boyuanxiao/SolarTracker/pcb/photodiode.sch

## KiCad design pcb/photodiode.sch (2017-03-01, an earlier design)

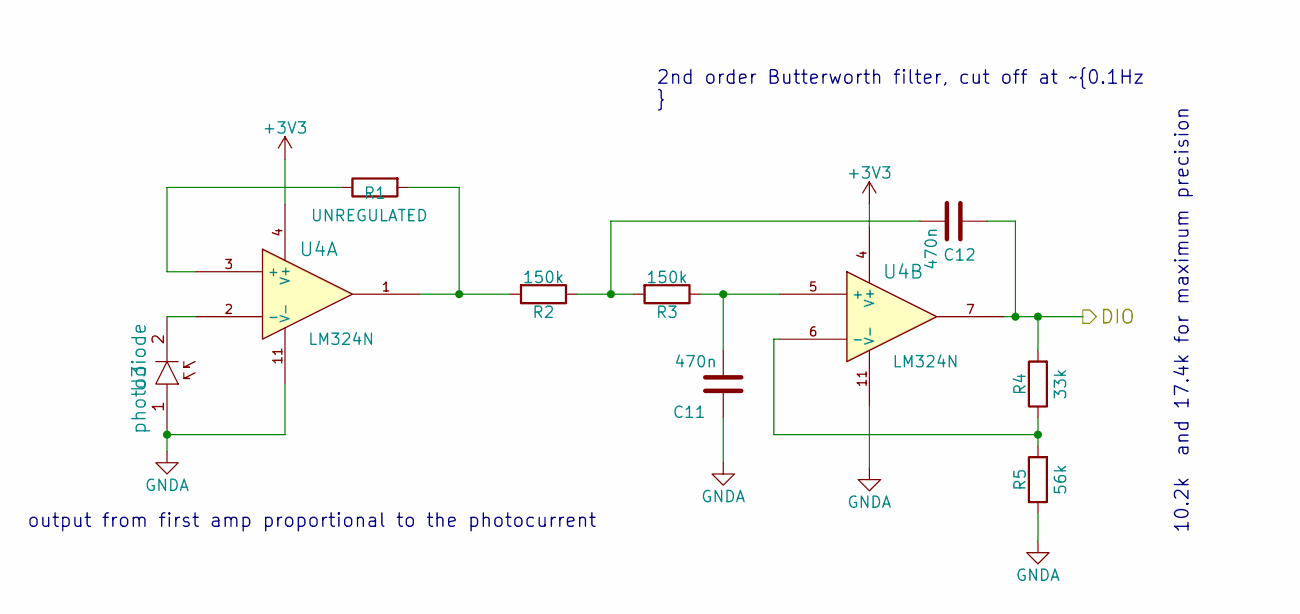
[picture p16: schematic photodiode.sch]

Parts:
C11, C16: 470n
R11: UNREGULATED
R12, R13: 150k
R14: 33k
R15: 56k
U6: photodiode
U7: LM324N

Connections:
+3V3: U7.4 (V+)
DIO: C16.1, R14.2, U7.7
GNDA: C11.1, R15.1, U6.1 (A), U7.11 (V-)
unnamed: C11.2, R13.1, U7.5 (+)
unnamed: C16.2, R12.1, R13.2
unnamed: R11.1, U7.3 (+)
unnamed: R11.2, R12.2, U7.1
unnamed: R14.1, R15.2, U7.6 (-)
unnamed: U6.2 (C), U7.2 (-)

Notes on the sheet:
2nd order Butterworth filter, cut off at ~0.1Hz
output from first amp proportional to the photocurrent
10.2k and 17.4k for maximum precision
