boyuanxiao/SolarTracker/pcb/solarTracker.sch

## KiCad design pcb/solarTracker.sch (2017-03-01, an earlier design)

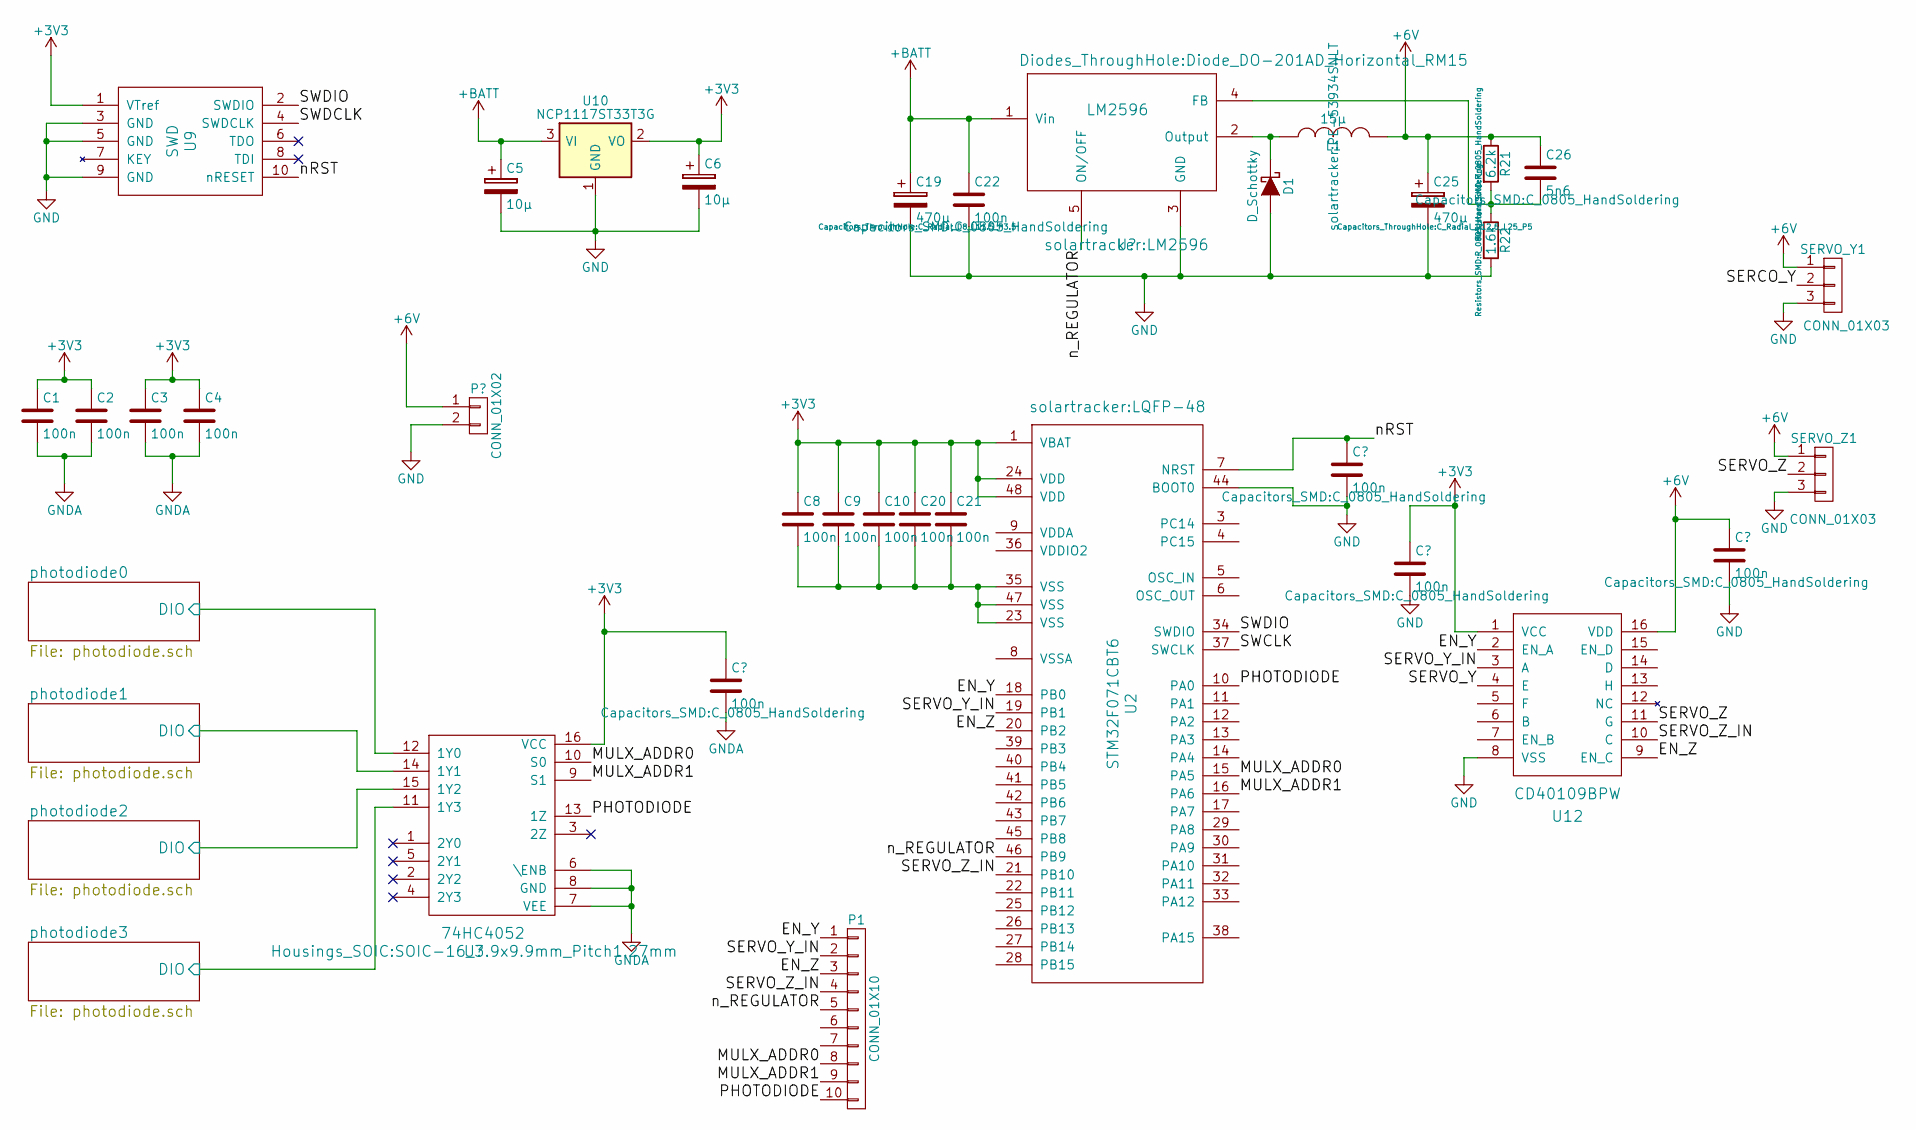
[picture p17: schematic solarTracker.sch]

Parts:
C1, C2, C3, C4, C8, C9, C10, C20, C21: 100n
C5, C6: 10µ
C19: 470µ; C_Radial_D8_L11.5_P3.5
C22: 100n; C_0805_HandSoldering
C25: 470µ; C_Radial_D12.5_L25_P5
C26: 5n6; C_0805_HandSoldering
D1: D_Schottky; Diode_DO-201AD_Horizontal_RM15
L1: 15µ; PE-53934SNLT
P1: CONN_01X10
R21: 6.2k; R_0805_HandSoldering
R22: 1.6k; R_0805_HandSoldering
SERVO_Y1: CONN_01X03
SERVO_Z1: CONN_01X03
U2: STM32F071CBT6; LQFP-48
U9: SWD
U10: NCP1117ST33T3G; SOT-223
U12: CD40109BPW; TSSOP-16-CD40190BPW

Connections:
+3V3: C1.1, C2.1, C3.1, C4.1, C6.1, C8.1, C9.1, C10.1, C20.1, C21.1, U2.1 (VBAT), U2.24 (VDD), U2.48 (VDD), U9.1 (VTref), U10.2 (VO), U12.1 (VCC)
+6V: C25.1, C26.1, L1.2, R21.1, SERVO_Y1.1, SERVO_Z1.1, U12.16 (VDD)
+BATT: C5.1, C19.1, C22.1, U10.3 (VI)
EN_Y: P1.1, U2.18 (PB0), U12.2 (EN_A)
EN_Z: P1.3, U2.20 (PB2), U12.9 (EN_C)
GND: C5.2, C6.2, C19.2, C22.2, C25.2, D1.2 (A), R22.2, SERVO_Y1.3, SERVO_Z1.3, U2.44 (BOOT0), U9.3 (GND), U9.5 (GND), U9.9 (GND), U10.1 (GND), U12.8 (VSS)
GNDA: C1.2, C2.2, C3.2, C4.2
MULX_ADDR0: P1.8, U2.15 (PA5)
MULX_ADDR1: P1.9, U2.16 (PA6)
unnamed: C8.2, C9.2, C10.2, C20.2, C21.2, U2.23 (VSS), U2.35 (VSS), U2.47 (VSS)
unnamed: C26.2, R21.2, R22.1
unnamed: D1.1 (K), L1.1
PHOTODIODE: P1.10, U2.10 (PA0)
SERCO_Y: SERVO_Y1.2
SERVO_Y: U12.4 (E)
SERVO_Y_IN: P1.2, U2.19 (PB1), U12.3 (A)
SERVO_Z: SERVO_Z1.2, U12.11 (G)
SERVO_Z_IN: P1.4, U2.21 (PB10), U12.10 (C)
SWCLK: U2.37 (SWCLK)
SWDCLK: U9.4 (SWDCLK)
SWDIO: U2.34 (SWDIO), U9.2 (SWDIO)
nRST: U2.7 (NRST), U9.10 (nRESET)
n_REGULATOR: P1.5, U2.46 (PB9)
